georgianailie109/TSC-EBookReader/Images/exploded_view.PNG

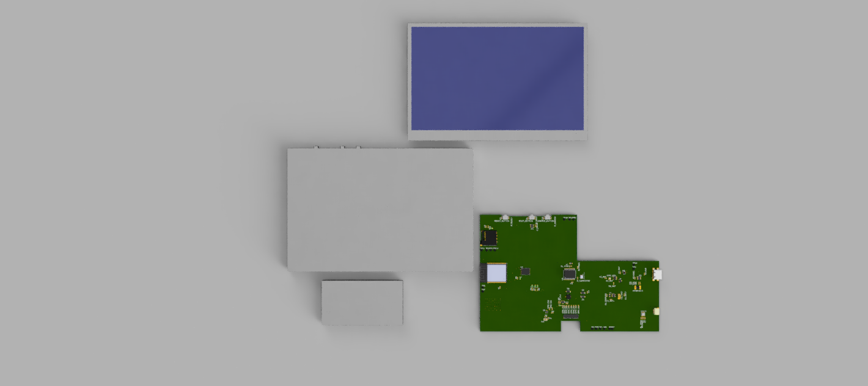
Images/exploded_view.PNG
