georgianailie109/TSC-EBookReader/Images/Screenshot 2025-04-14 140006.png

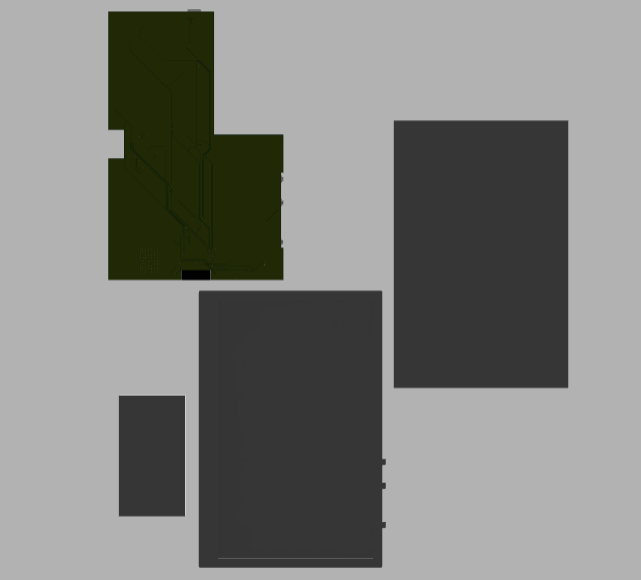
Images/Screenshot 2025-04-14 140006.png
