georgianailie109/TSC-EBookReader/Images/Screenshot 2025-04-14 140417.png

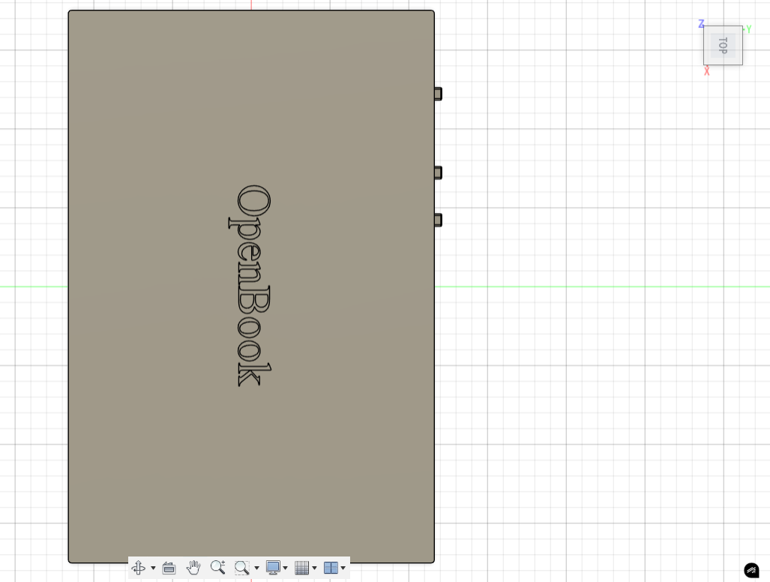
Images/Screenshot 2025-04-14 140417.png
