georgianailie109/TSC-EBookReader/Images/Screenshot 2025-04-14 141112.png

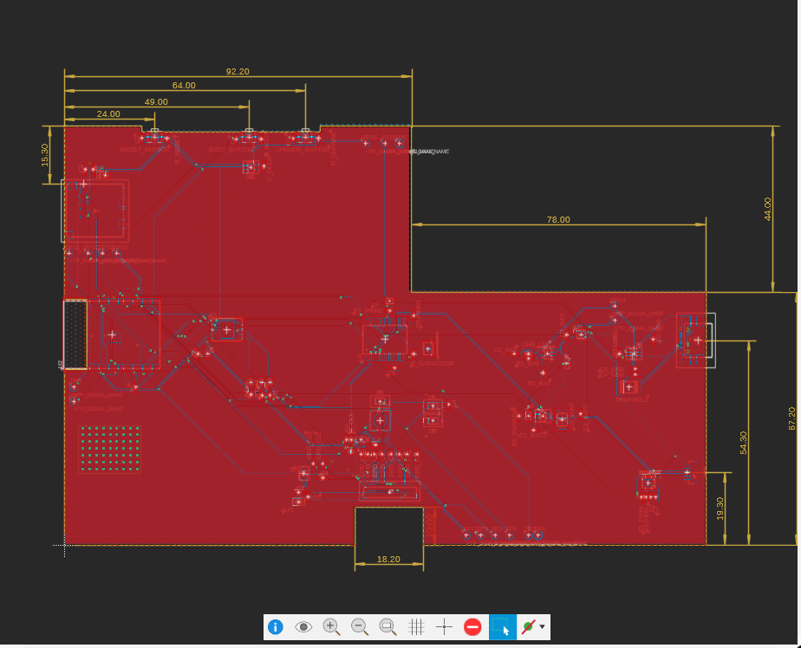
Images/Screenshot 2025-04-14 141112.png
