georgianailie109/TSC-EBookReader/Images/Screenshot 2025-04-14 141750.png

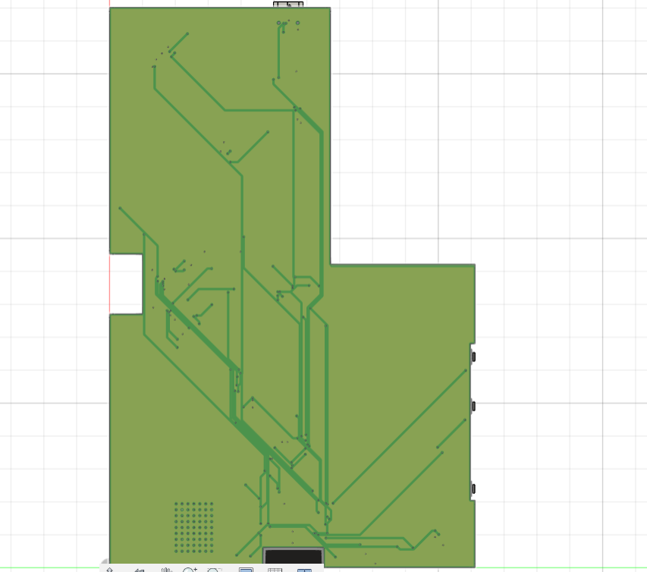
Images/Screenshot 2025-04-14 141750.png
